dheera/shoji-lamps/images/shoji0.jpg

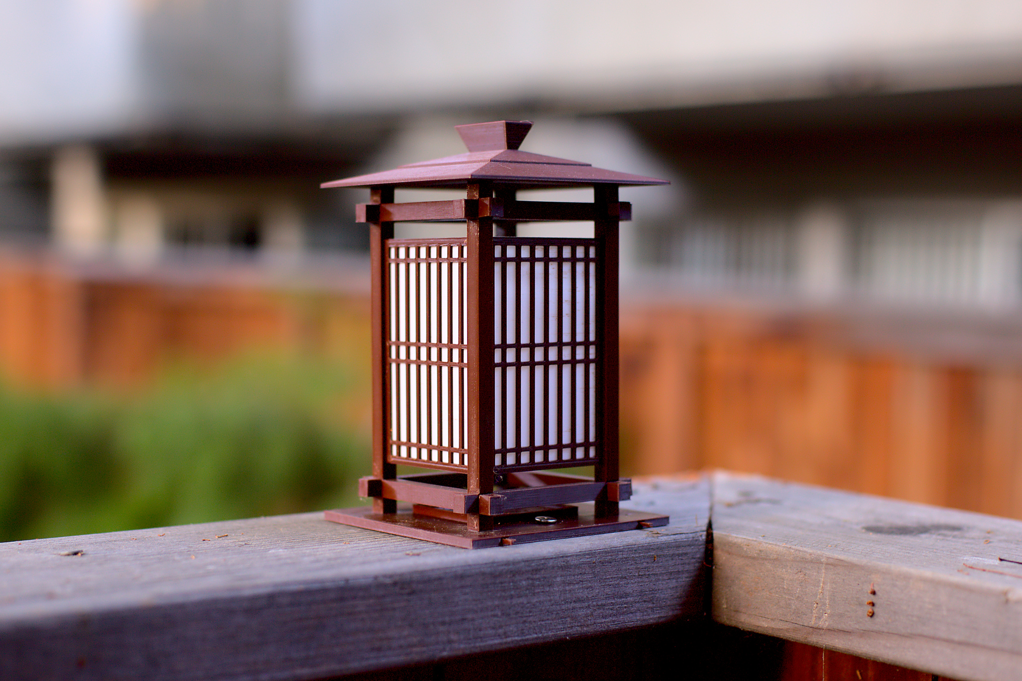
images/shoji0.jpg
